giltesa/Stair-Light-Controller/2. Gerbers/1. Stair Light - Controller/v1.0/Images/Controller bottom.jpg

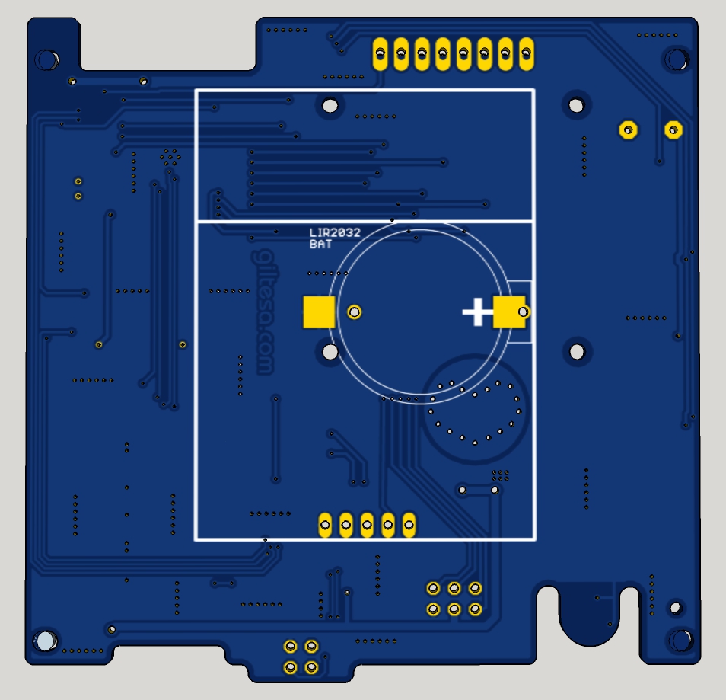
2. Gerbers/1. Stair Light - Controller/v1.0/Images/Controller bottom.jpg
