giltesa/Stair-Light-Controller/2. Gerbers/1. Stair Light - Controller/v1.0/Images/stair light controller.GBL.png

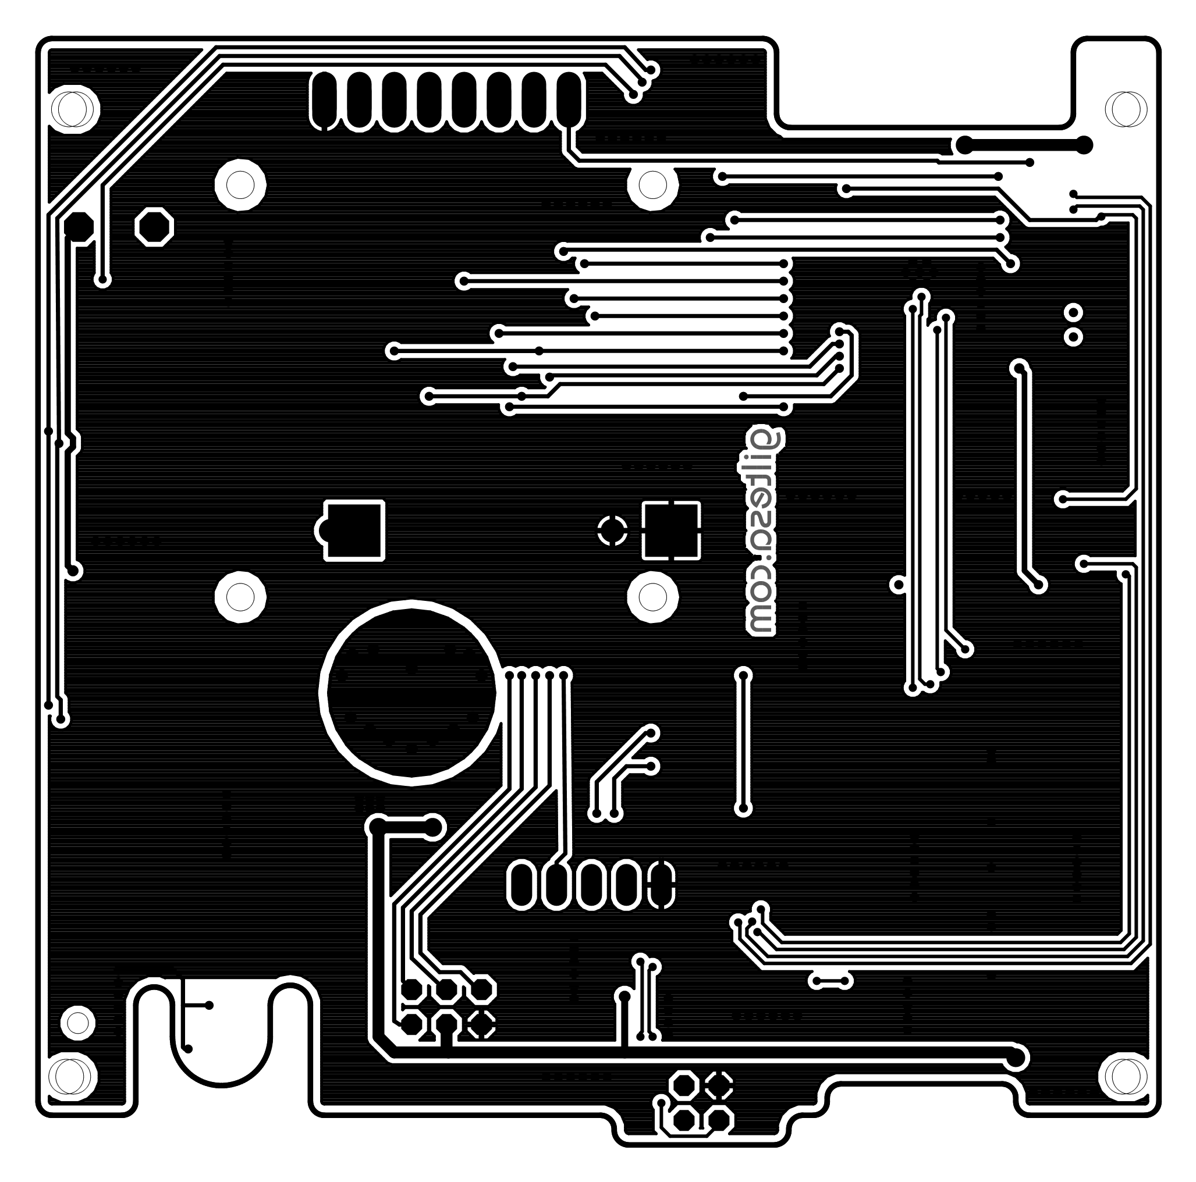
2. Gerbers/1. Stair Light - Controller/v1.0/Images/stair light controller.GBL.png
