giltesa/Stair-Light-Controller/2. Gerbers/1. Stair Light - Controller/v1.0/Images/stair light controller.GBS.png

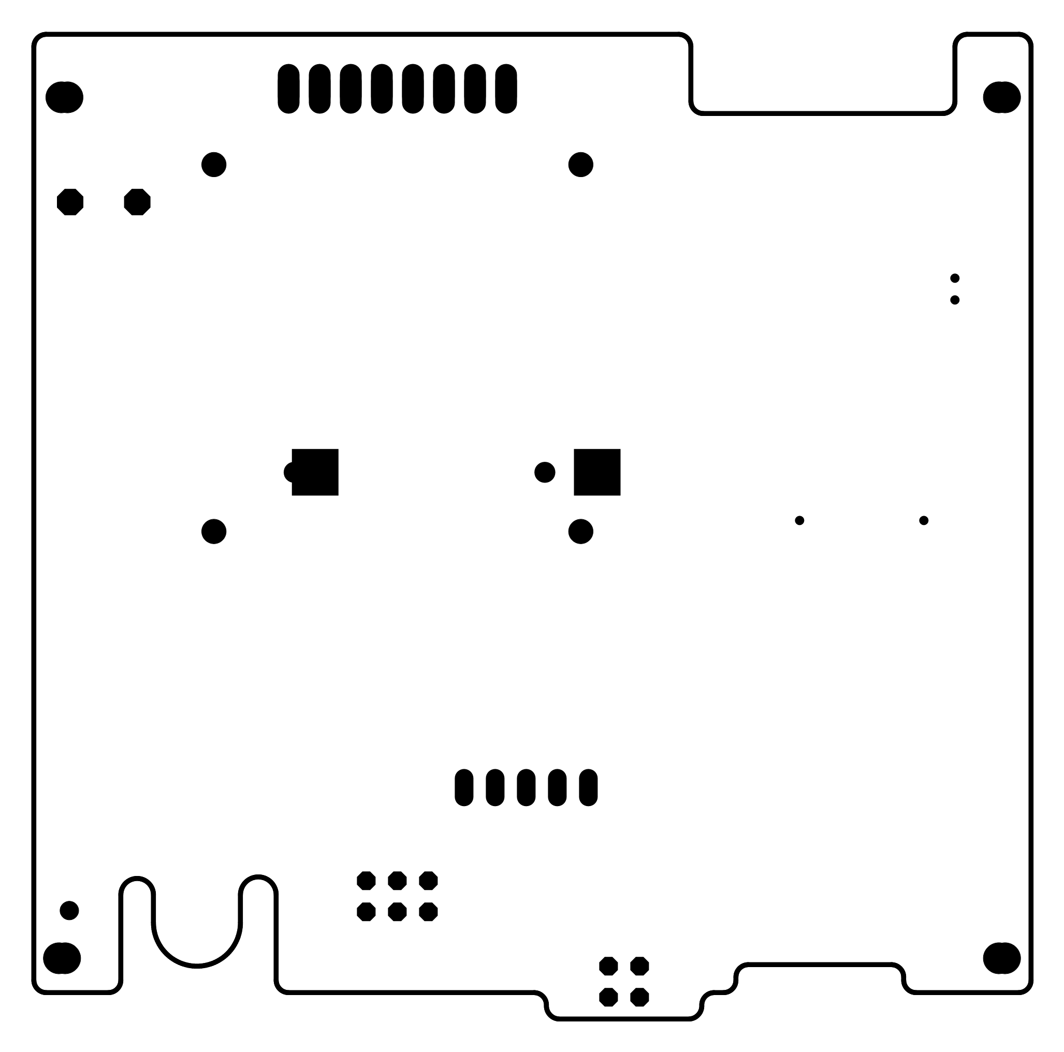
2. Gerbers/1. Stair Light - Controller/v1.0/Images/stair light controller.GBS.png
