giltesa/Stair-Light-Controller/2. Gerbers/1. Stair Light - Controller/v1.0/Images/stair light controller.GTL.png

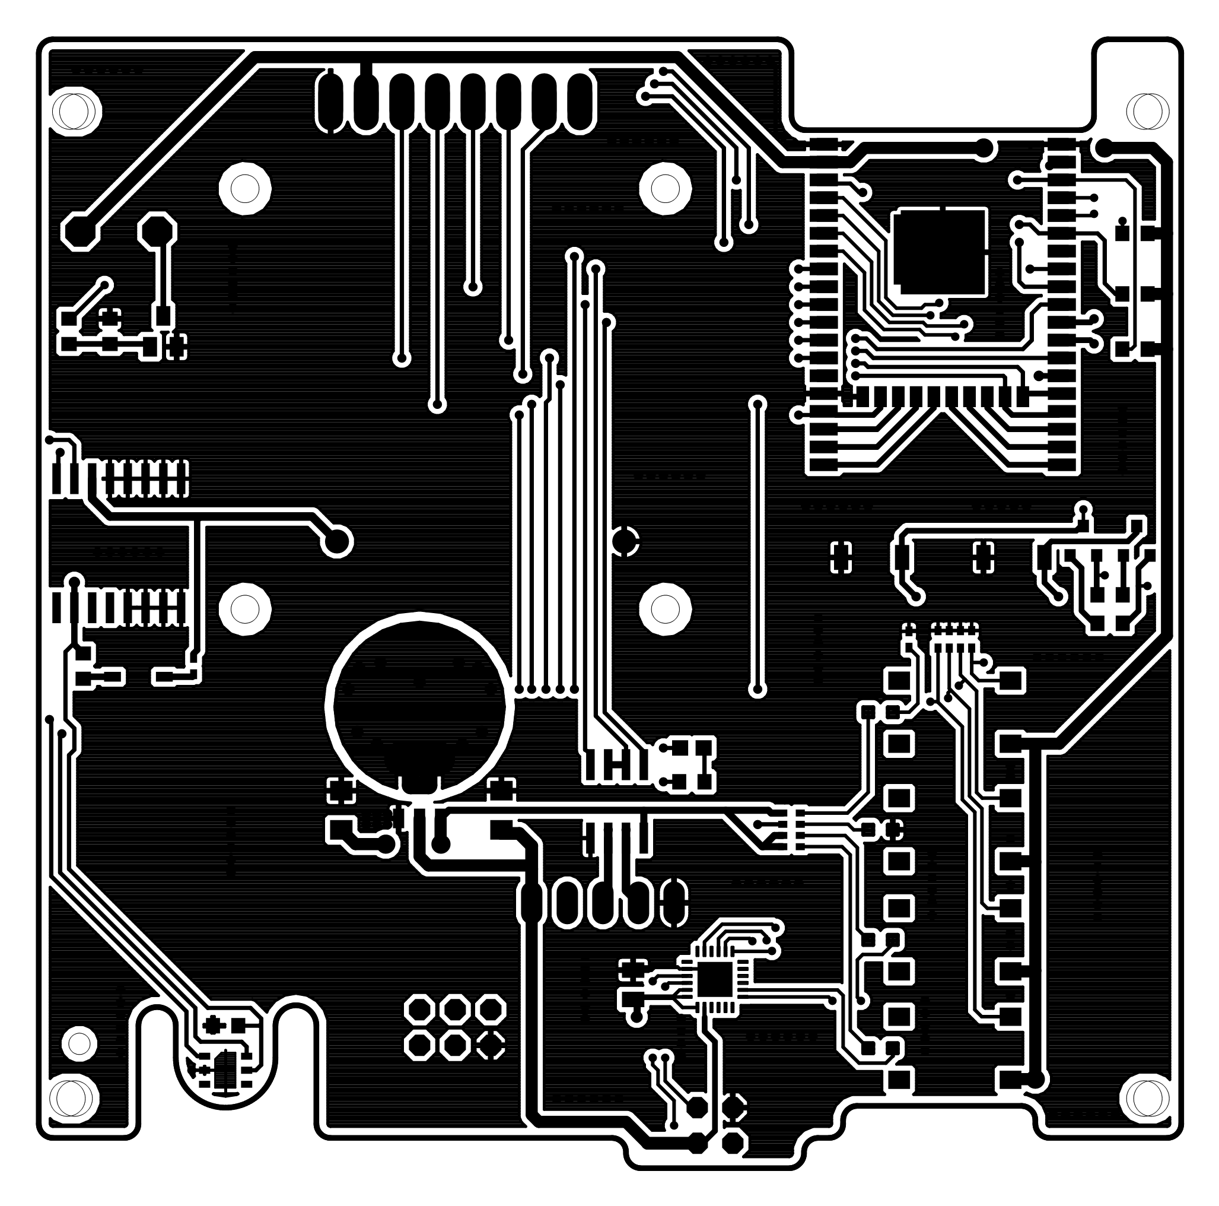
2. Gerbers/1. Stair Light - Controller/v1.0/Images/stair light controller.GTL.png
