giltesa/Stair-Light-Controller/2. Gerbers/2. Stair Light - USB/v1.0/Images/stair light usb.GML.png

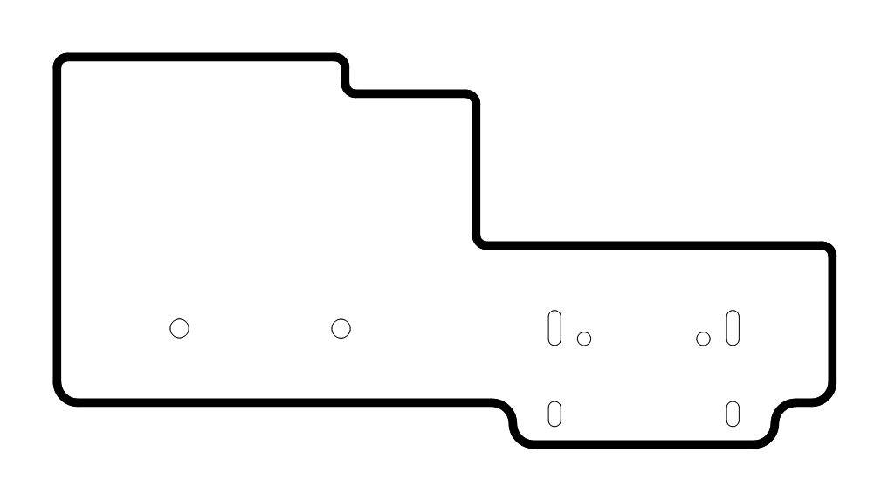
2. Gerbers/2. Stair Light - USB/v1.0/Images/stair light usb.GML.png
