giltesa/Stair-Light-Controller/2. Gerbers/3. Stair Light - PSU/v1.0/Images/PSU bottom.jpg

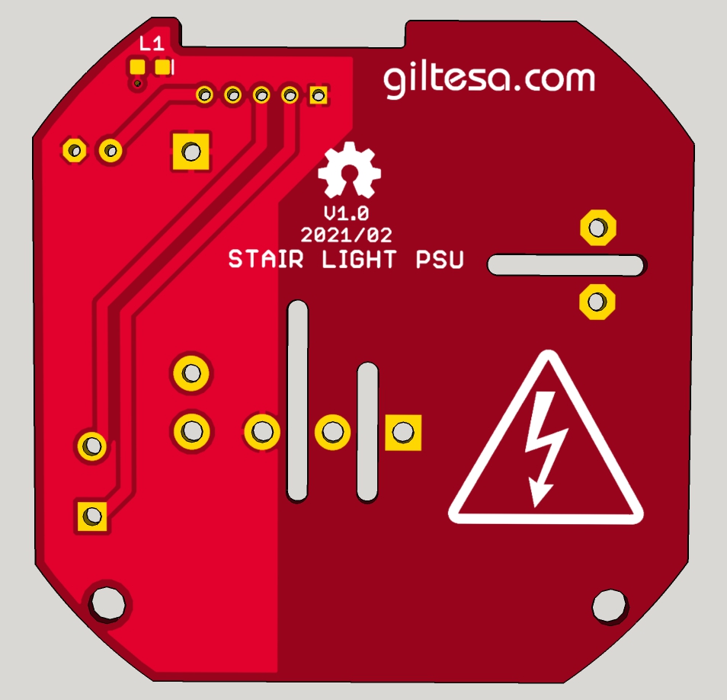
2. Gerbers/3. Stair Light - PSU/v1.0/Images/PSU bottom.jpg
