giltesa/Stair-Light-Controller/2. Gerbers/3. Stair Light - PSU/v1.0/Images/stair light psu.GBO.png

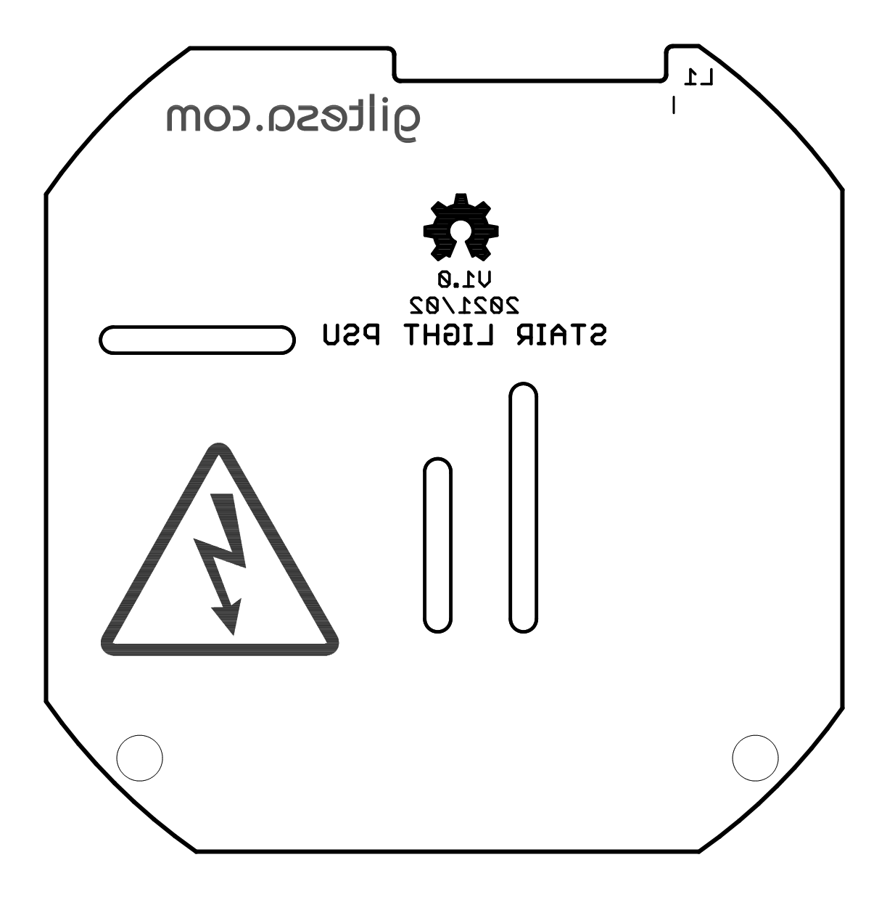
2. Gerbers/3. Stair Light - PSU/v1.0/Images/stair light psu.GBO.png
