giltesa/Stair-Light-Controller/3. Documentation/BHT-100GA - Plastic case/BHT-100GA_2.jpg

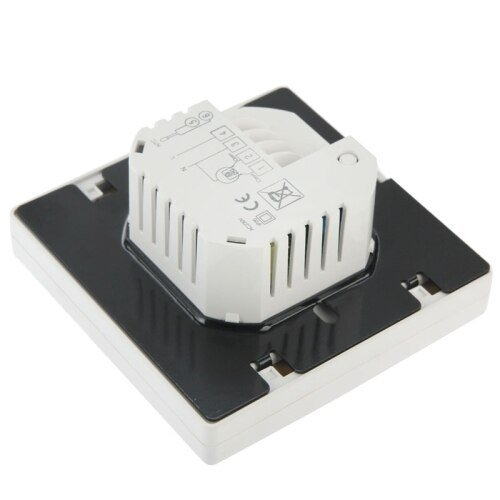
3. Documentation/BHT-100GA - Plastic case/BHT-100GA_2.jpg
