giltesa/Stair-Light-Controller/3. Documentation/BHT-100GA - Plastic case/BHT-100GA_4.jpg

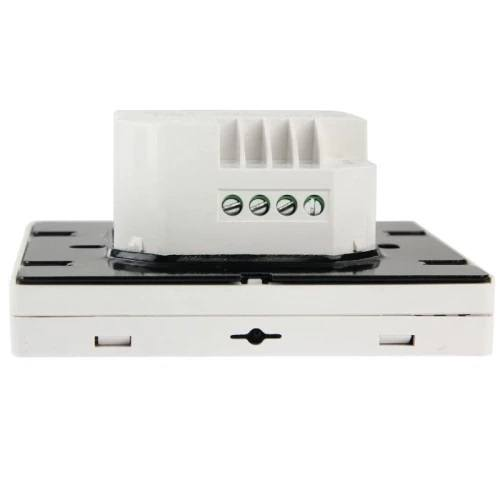
3. Documentation/BHT-100GA - Plastic case/BHT-100GA_4.jpg
