giltesa/Stair-Light-Controller/3. Documentation/ESP32/c612ebde-27de-4a74-b6ca-7758806fee53.png

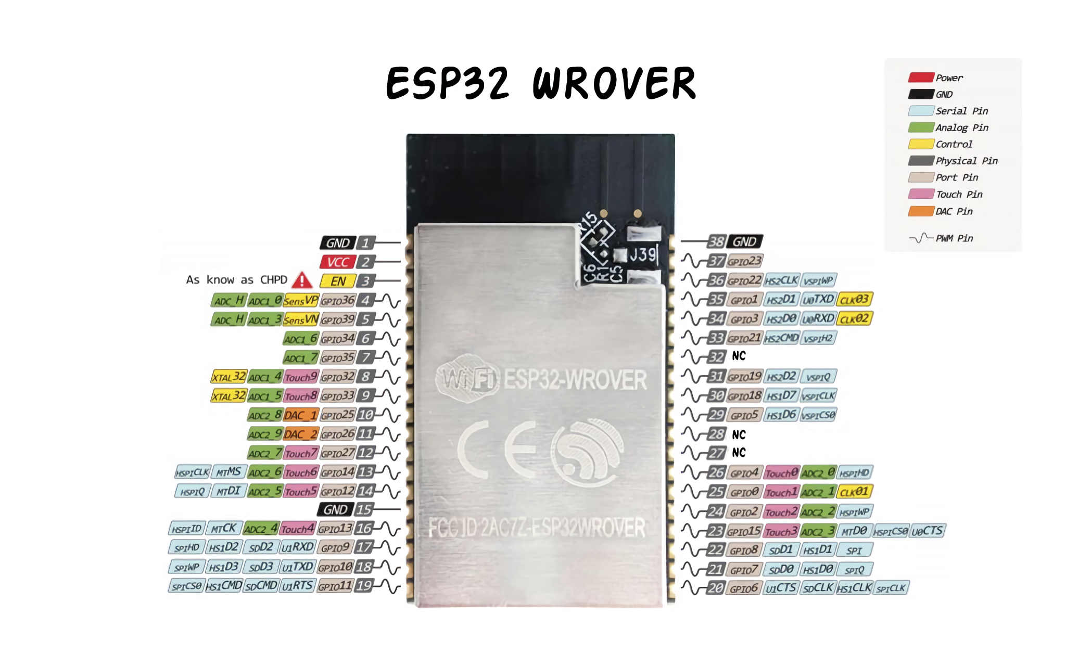
3. Documentation/ESP32/c612ebde-27de-4a74-b6ca-7758806fee53.png
