giltesa/Stair-Light-Controller/3. Documentation/ESP32/Hd4c6a8329b5f432baead7a3c7b3683116.webp

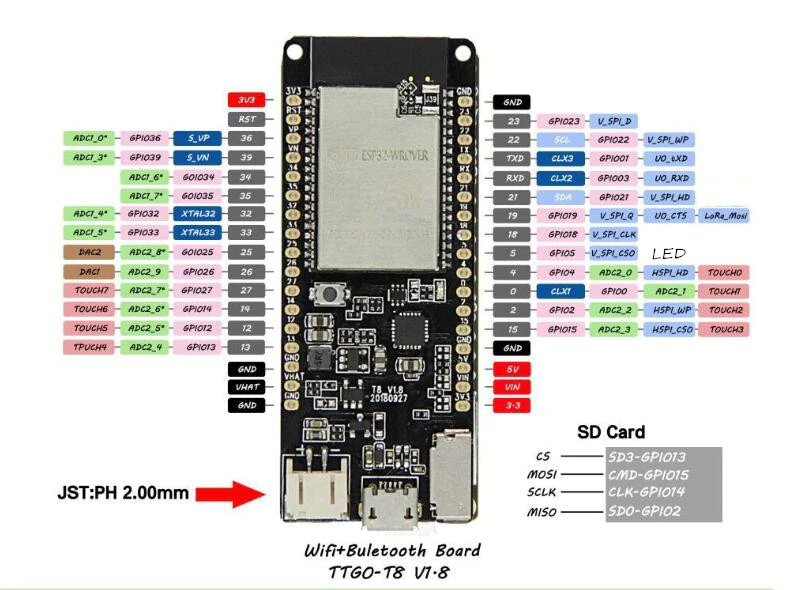
3. Documentation/ESP32/Hd4c6a8329b5f432baead7a3c7b3683116.webp
