giltesa/Stair-Light-Controller/3. Documentation/HT7333 - Linear Voltage Regulator/HT7333-Application-Circuit_0.PNG

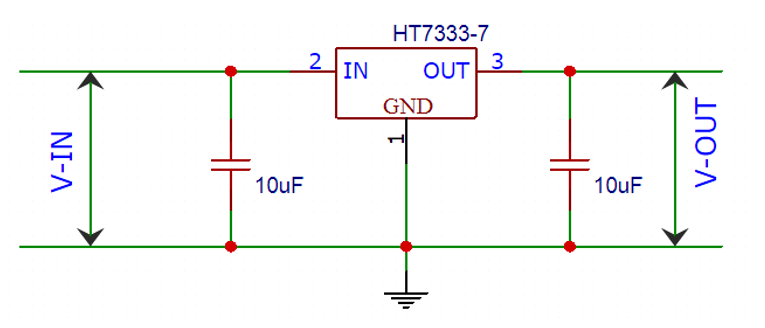
3. Documentation/HT7333 - Linear Voltage Regulator/HT7333-Application-Circuit_0.PNG
