giltesa/Stair-Light-Controller/3. Documentation/PSU board/Image (10).jpg

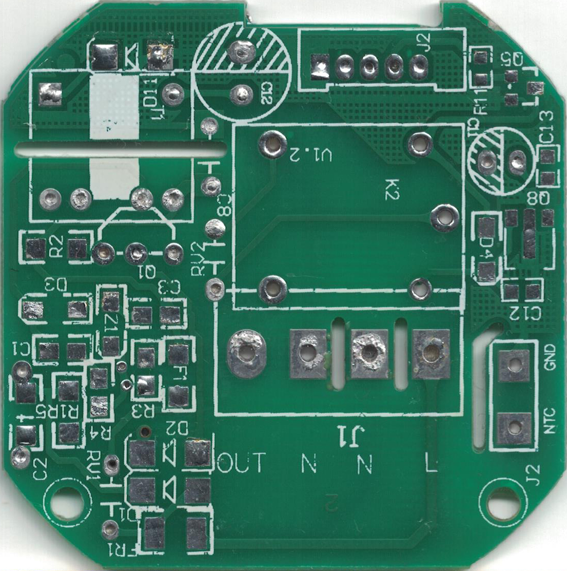
3. Documentation/PSU board/Image (10).jpg
