giltesa/Stair-Light-Controller/3. Documentation/PSU board/psu.bmp

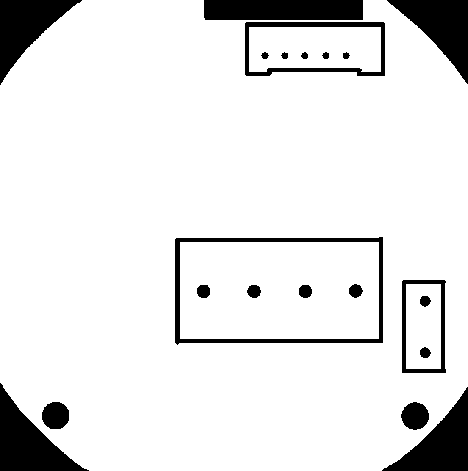
3. Documentation/PSU board/psu.bmp
