giltesa/Stair-Light-Controller/3. Documentation/SD/sdcard.png

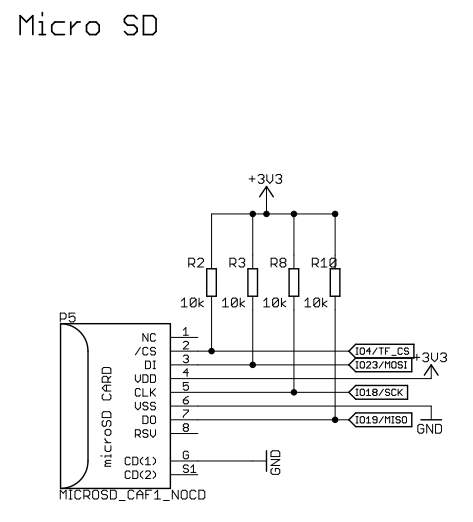
3. Documentation/SD/sdcard.png
