giltesa/Stair-Light-Controller/3. Documentation/TFT/H8d0c5012b2ea4059b8d0e503878c055fy.webp

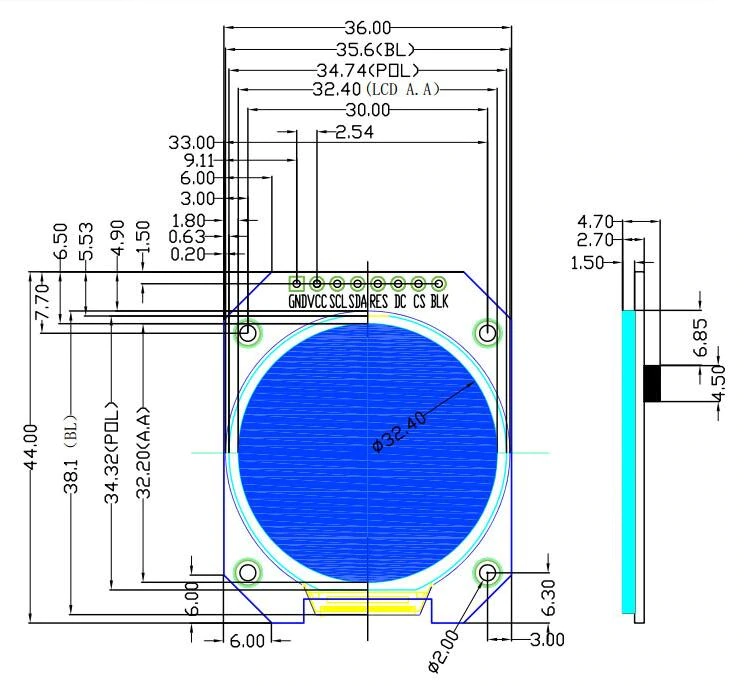
3. Documentation/TFT/H8d0c5012b2ea4059b8d0e503878c055fy.webp
