giltesa/Stair-Light-Controller/3. Documentation/VL53L1X/Side-by-side-comparison-of-the-VL6180X.-VL53L0X.-and-VL53L1X-Time-of-Flight-Distance-Sensor-Carriers..jpg

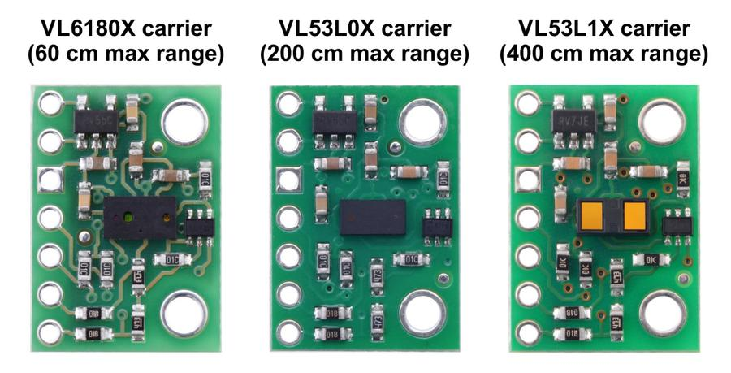
3. Documentation/VL53L1X/Side-by-side-comparison-of-the-VL6180X.-VL53L0X.-and-VL53L1X-Time-of-Flight-Distance-Sensor-Carriers..jpg
